yasaitanmen/Speaker-Enclosure/cad/stl/port_tube_150mm.stl

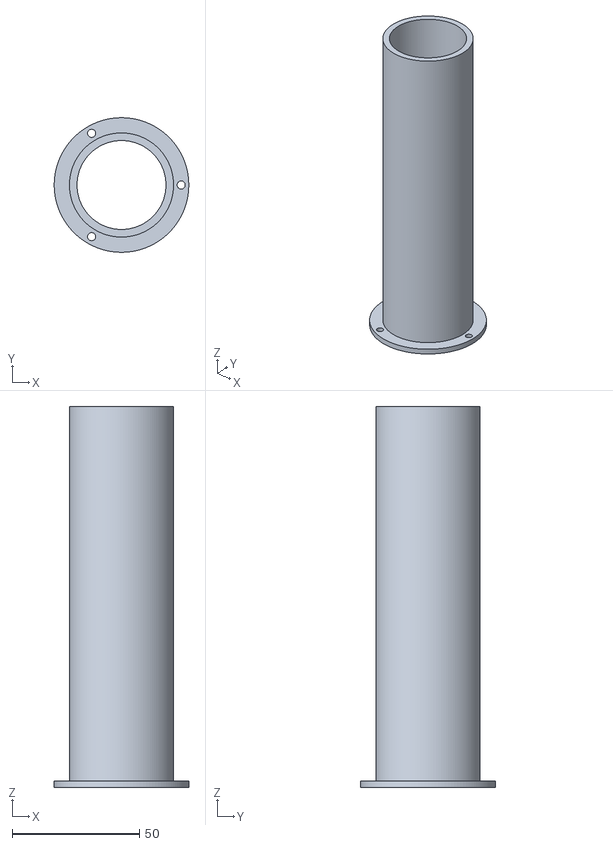
[picture p16: CAD file, 2026-08-31]
cad/stl/port_tube_150mm.stl
53.0 x 53.0 x 150.0
