yasaitanmen/Speaker-Enclosure/cad/stl/5.5L/upper_plate_u4_blank.stl

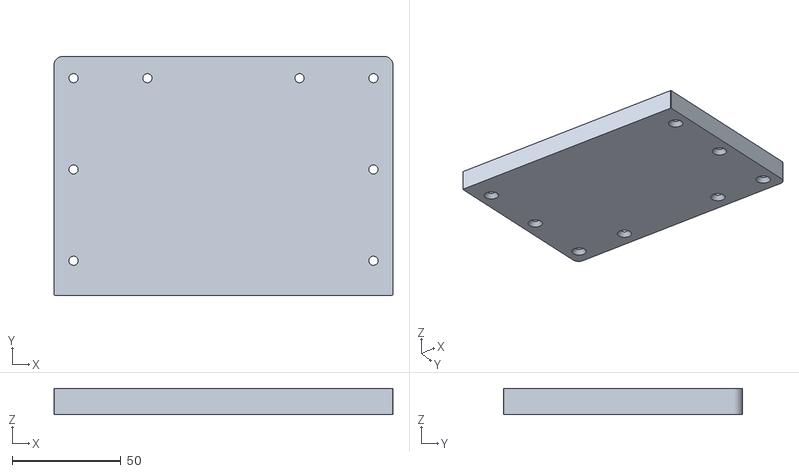
[picture p17: CAD file, 2026-08-31]
cad/stl/5.5L/upper_plate_u4_blank.stl
156.0 x 110.0 x 12.0
