yasaitanmen/Speaker-Enclosure/cad/stl/upper_plate_u2_3inch.stl

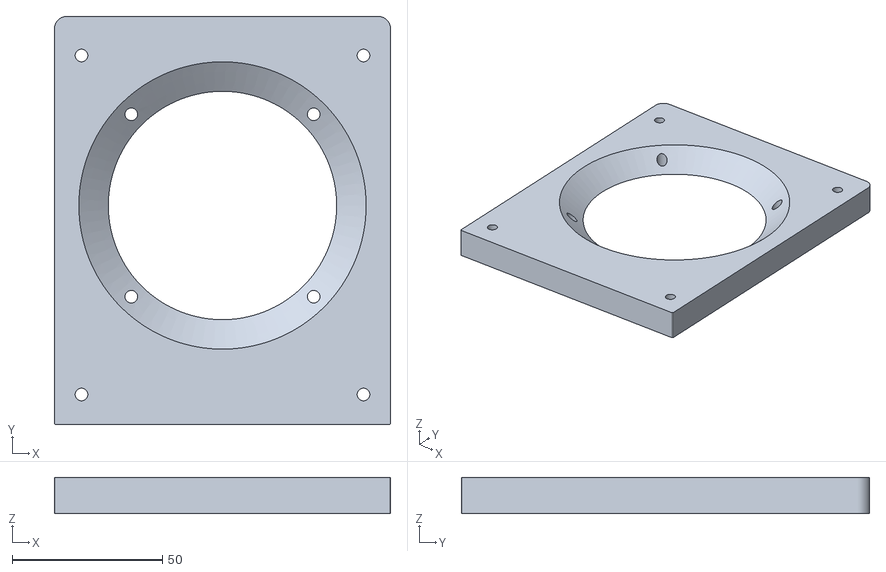
[picture p18: CAD file, 2026-08-31]
cad/stl/upper_plate_u2_3inch.stl
112.0 x 136.0 x 12.0
