yasaitanmen/Speaker-Enclosure/cad/stl/5.5L/upper_plate_u3_4inch.stl

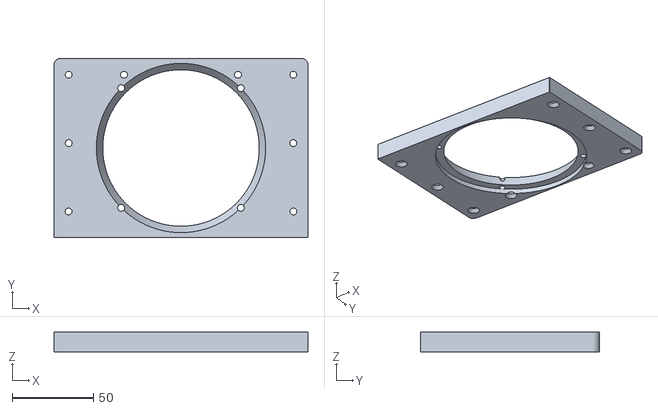
[picture p19: CAD file, 2026-08-31]
cad/stl/5.5L/upper_plate_u3_4inch.stl
156.0 x 110.0 x 12.0
