yasaitanmen/Speaker-Enclosure/cad/stl/port_tube_80mm.stl

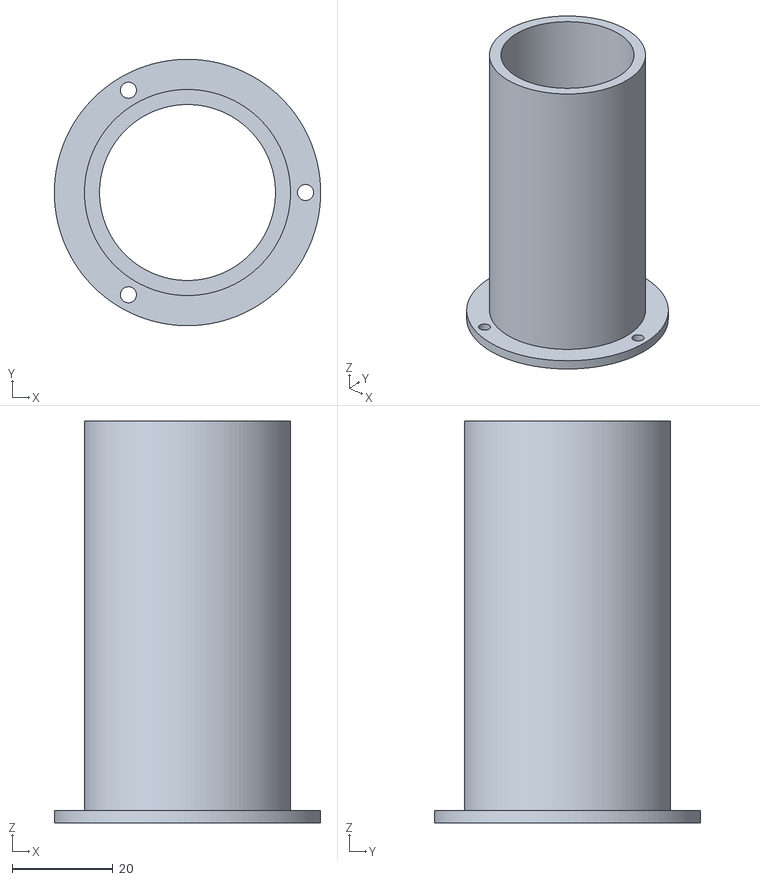
[picture p20: CAD file, 2026-08-31]
cad/stl/port_tube_80mm.stl
53.0 x 53.0 x 80.0
