yasaitanmen/Speaker-Enclosure/cad/stl/upper_gasket_eva.stl

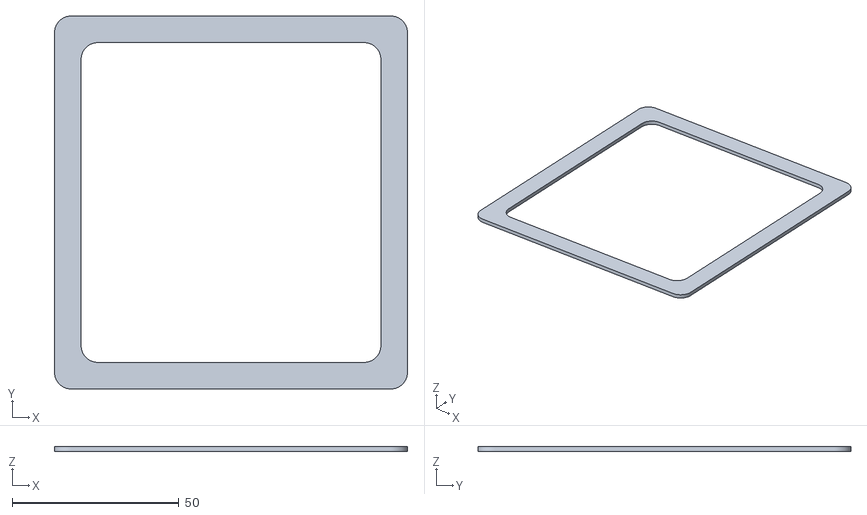
[picture p22: CAD file, 2026-08-31]
cad/stl/upper_gasket_eva.stl
106.0 x 112.0 x 1.50
