yasaitanmen/Speaker-Enclosure/cad/stl/upper_plate_u1_2inch.stl

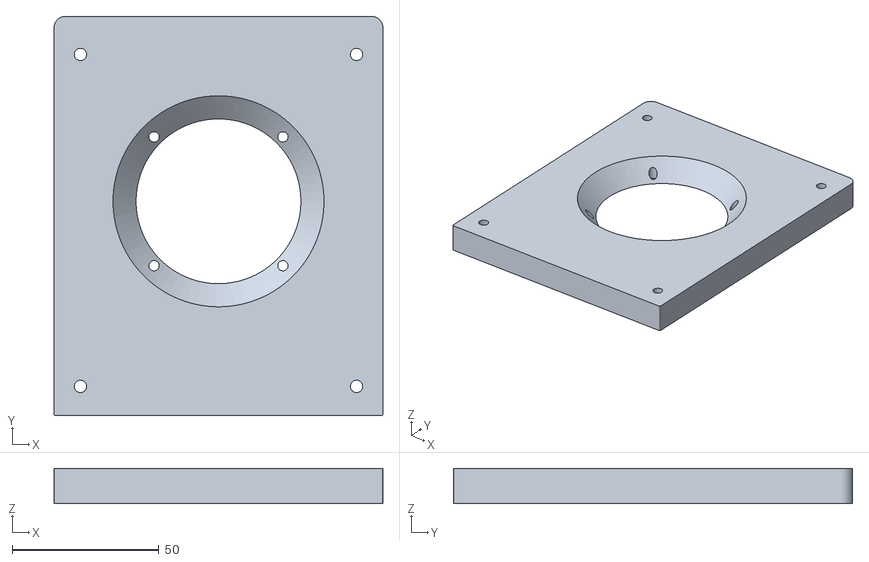
[picture p24: CAD file, 2026-08-31]
cad/stl/upper_plate_u1_2inch.stl
112.0 x 136.0 x 12.0
