yasaitanmen/Speaker-Enclosure/cad/stl/5.5L/lower_plate_55L_p3_slit_port.stl

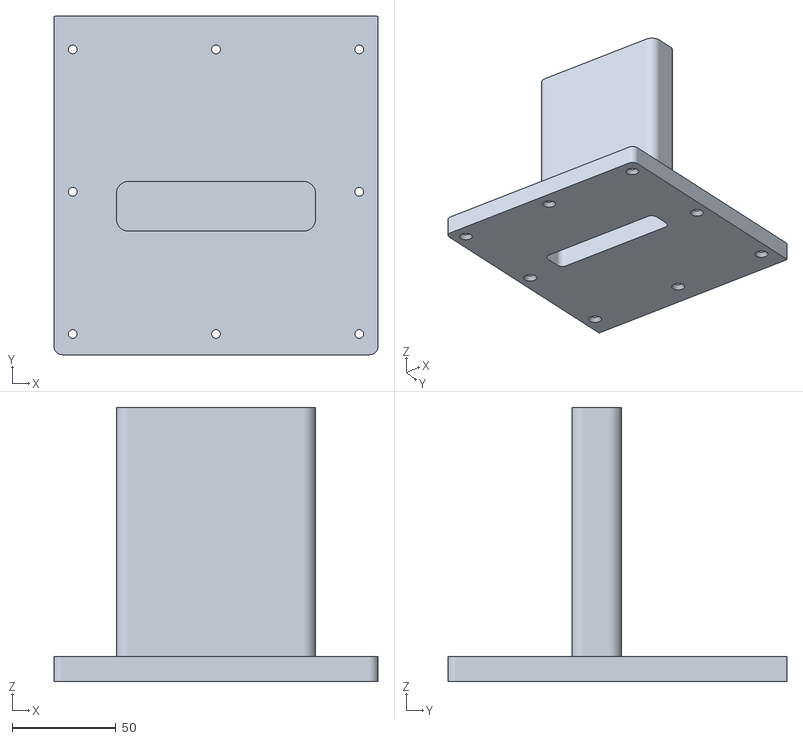
[picture p25: CAD file, 2026-08-31]
cad/stl/5.5L/lower_plate_55L_p3_slit_port.stl
156.0 x 163.0 x 132.0
