yasaitanmen/Speaker-Enclosure/cad/stl/window_brace.stl

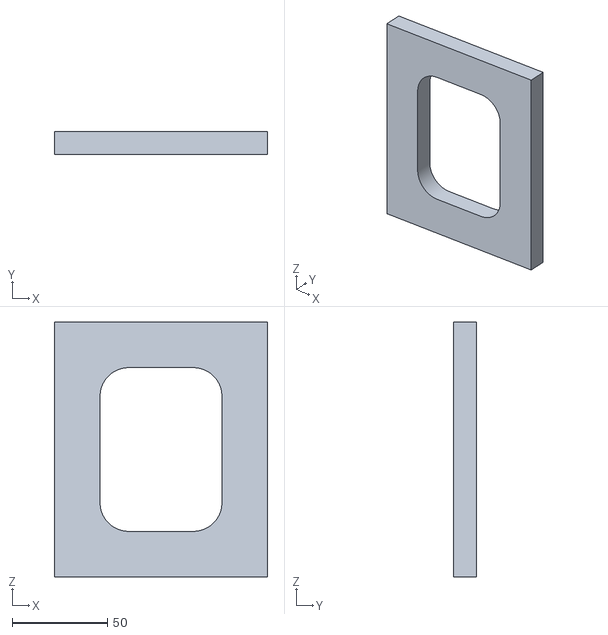
[picture p26: CAD file, 2026-08-31]
cad/stl/window_brace.stl
112.0 x 12.0 x 134.0
