yasaitanmen/Speaker-Enclosure/cad/stl/inner_fixed_baffle_frame.stl

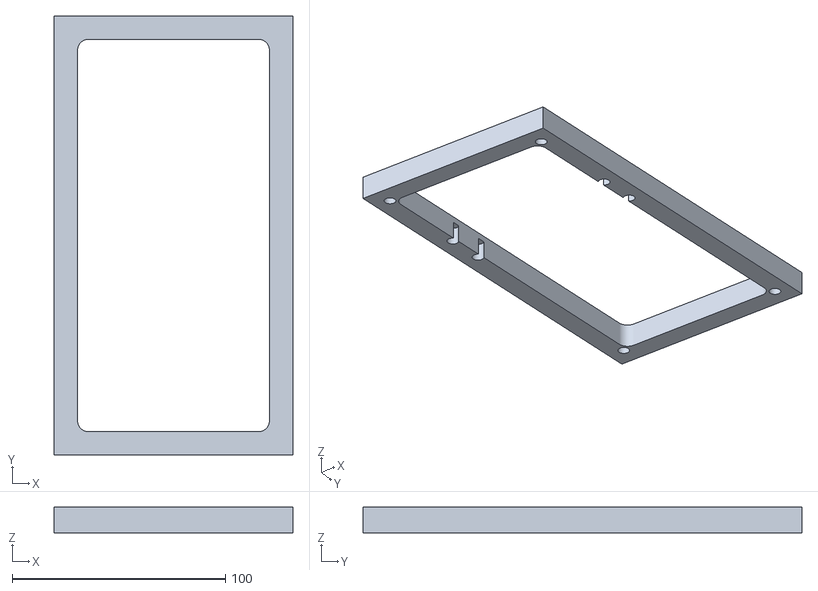
[picture p28: CAD file, 2026-08-31]
cad/stl/inner_fixed_baffle_frame.stl
112.0 x 206.0 x 12.0
