yasaitanmen/Speaker-Enclosure/cad/stl/5.5L/lower_plate_55L_p4_passive_rad.stl

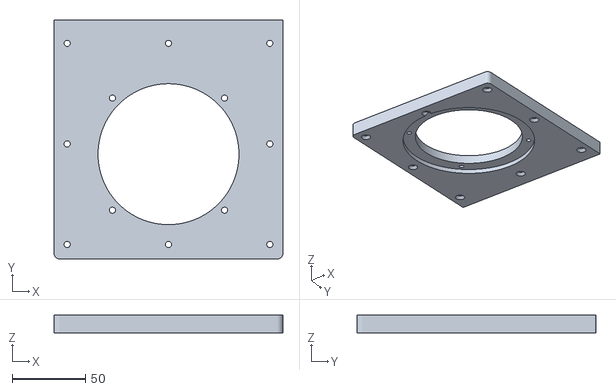
[picture p29: CAD file, 2026-08-31]
cad/stl/5.5L/lower_plate_55L_p4_passive_rad.stl
156.0 x 163.0 x 12.0
