yasaitanmen/Speaker-Enclosure/cad/stl/rear_panel.stl

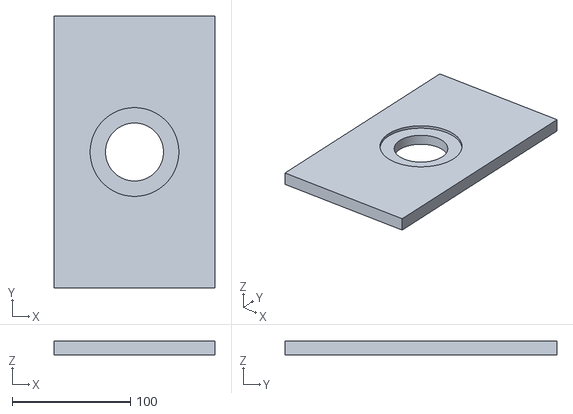
[picture p30: CAD file, 2026-08-31]
cad/stl/rear_panel.stl
136.0 x 230.0 x 12.0
