yasaitanmen/Speaker-Enclosure/cad/stl/lower_gasket_eva.stl

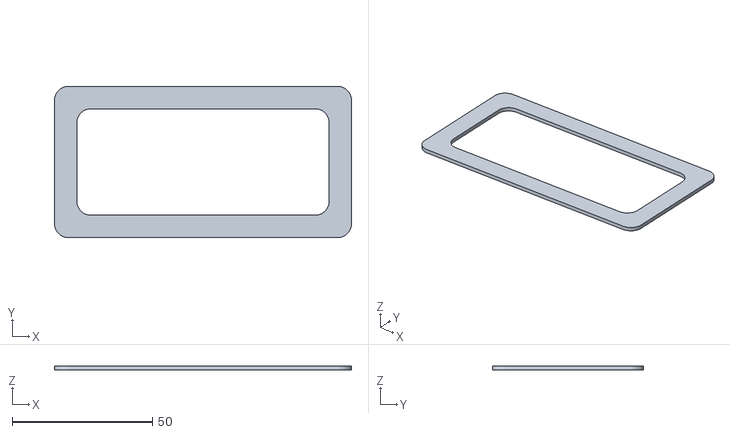
[picture p31: CAD file, 2026-08-31]
cad/stl/lower_gasket_eva.stl
106.0 x 54.0 x 1.50
