yasaitanmen/Speaker-Enclosure/cad/stl/5.5L/internal_hollow_mouth_frame.stl

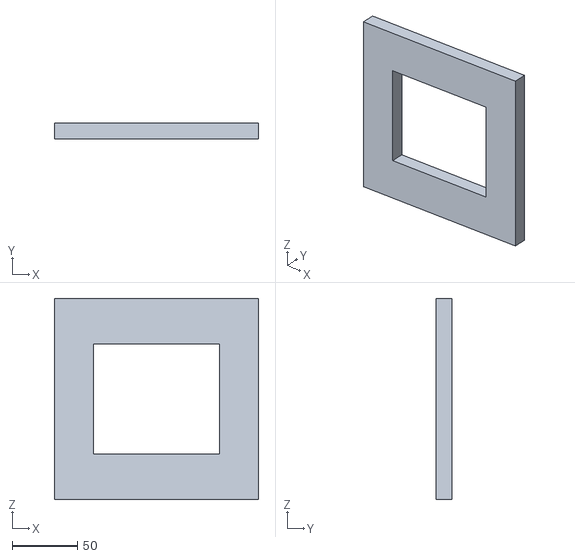
[picture p32: CAD file, 2026-08-31]
cad/stl/5.5L/internal_hollow_mouth_frame.stl
156.0 x 12.0 x 154.0
