yasaitanmen/Speaker-Enclosure/cad/stl/5.5L/removable_dbr_partition_plate.stl

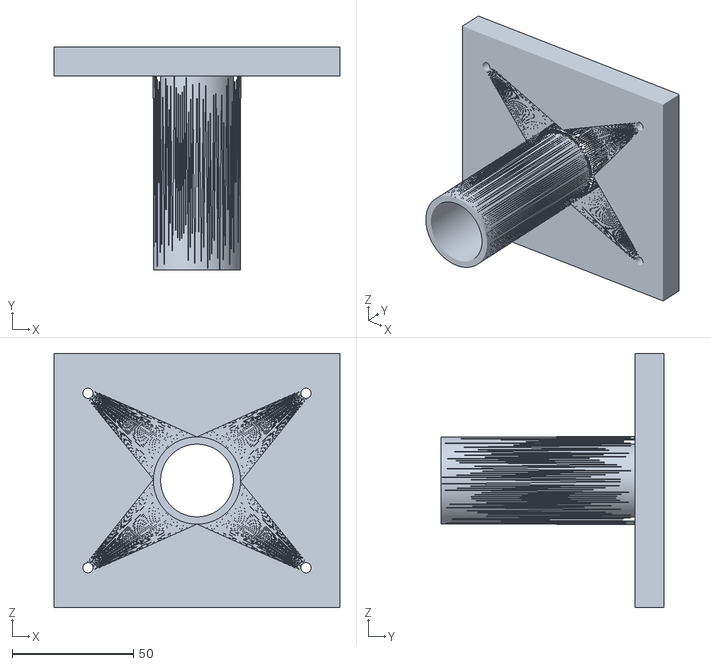
[picture p33: CAD file, 2026-08-31]
cad/stl/5.5L/removable_dbr_partition_plate.stl
118.0 x 92.0 x 105.0
