yasaitanmen/Speaker-Enclosure/cad/stl/lower_plate_p3_slit_port.stl

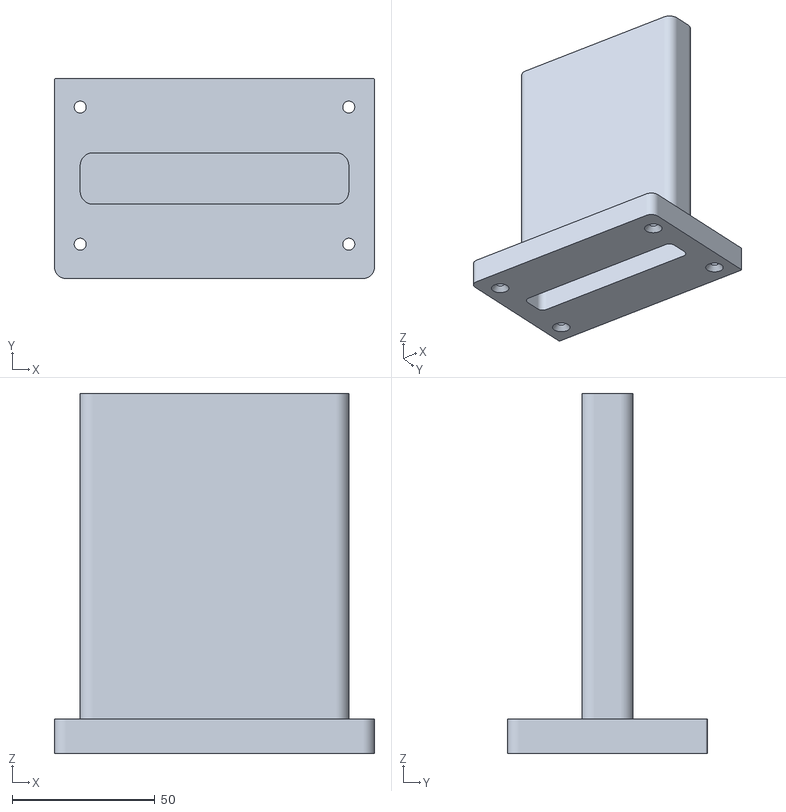
[picture p34: CAD file, 2026-08-31]
cad/stl/lower_plate_p3_slit_port.stl
112.0 x 70.0 x 126.0
