yasaitanmen/Speaker-Enclosure/cad/stl/5.5L/internal_dbr_partition_brace.stl

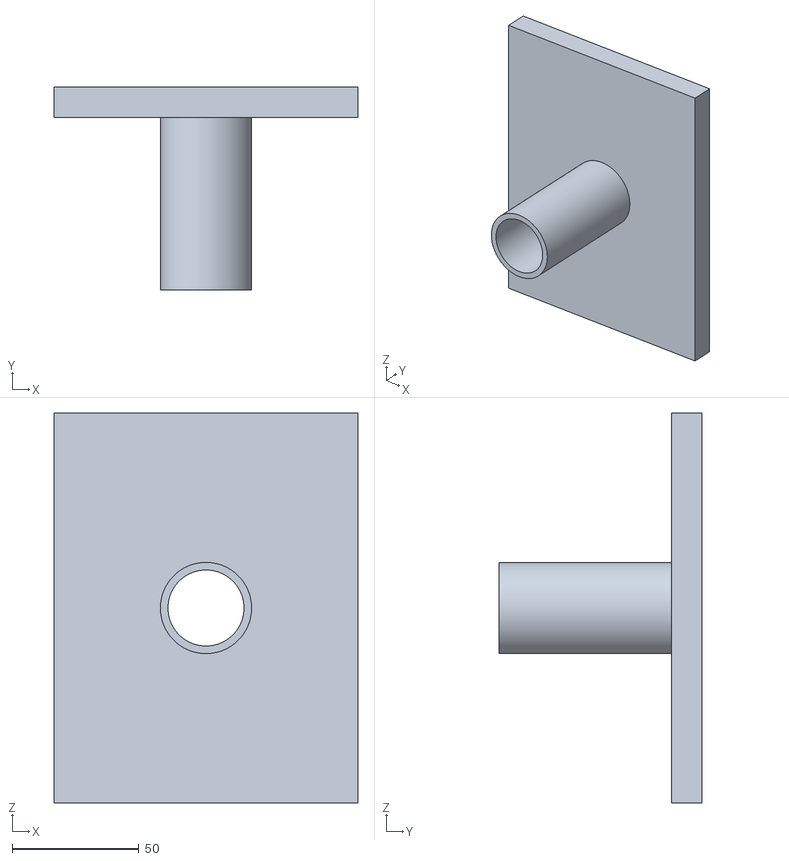
[picture p35: CAD file, 2026-08-31]
cad/stl/5.5L/internal_dbr_partition_brace.stl
120.0 x 80.0 x 154.0
