yasaitanmen/Speaker-Enclosure/cad/stl/upper_plate_u4_blank.stl

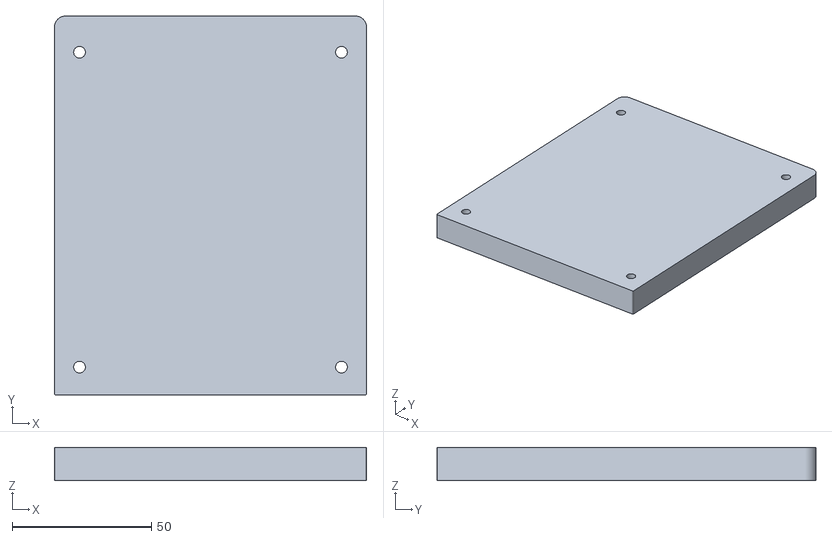
[picture p36: CAD file, 2026-08-31]
cad/stl/upper_plate_u4_blank.stl
112.0 x 136.0 x 12.0
