yasaitanmen/Speaker-Enclosure/cad/stl/5.5L/inner_ladder_baffle_frame_55L.stl

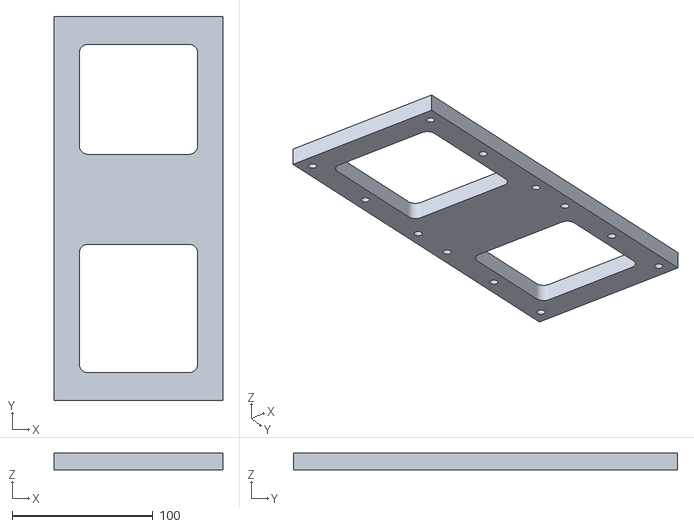
[picture p37: CAD file, 2026-08-31]
cad/stl/5.5L/inner_ladder_baffle_frame_55L.stl
120.0 x 273.0 x 12.0
