yasaitanmen/Speaker-Enclosure/cad/stl/5.5L/ladder_frame_gasket_55L_eva.stl

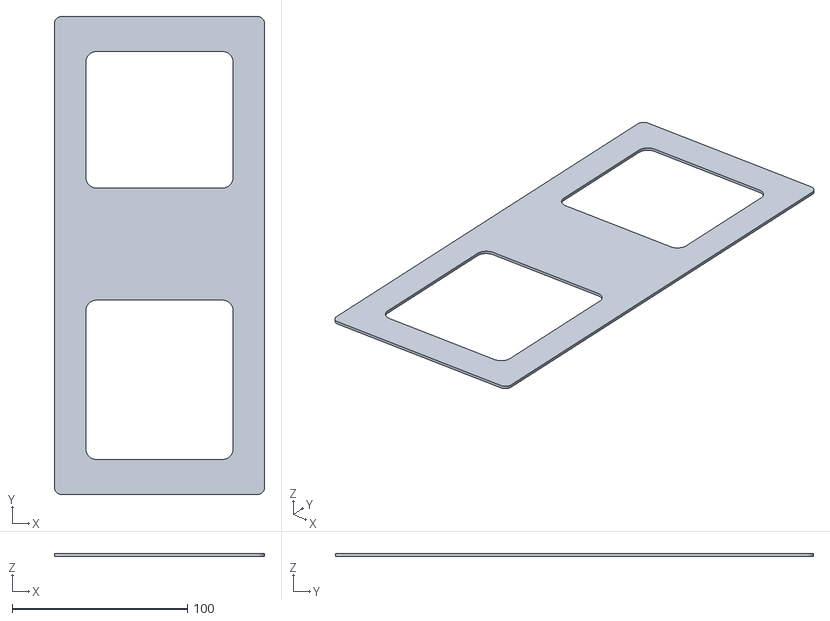
[picture p38: CAD file, 2026-08-31]
cad/stl/5.5L/ladder_frame_gasket_55L_eva.stl
120.0 x 273.0 x 1.50
