yasaitanmen/Speaker-Enclosure/cad/stl/lower_plate_p4_passive_rad.stl

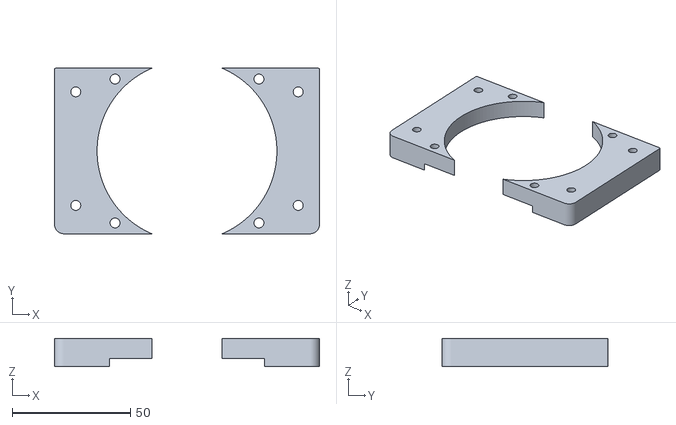
[picture p39: CAD file, 2026-08-31]
cad/stl/lower_plate_p4_passive_rad.stl
112.0 x 70.0 x 12.0
