yasaitanmen/Speaker-Enclosure/cad/stl/5.5L/port_tube_45mm_120mm.stl

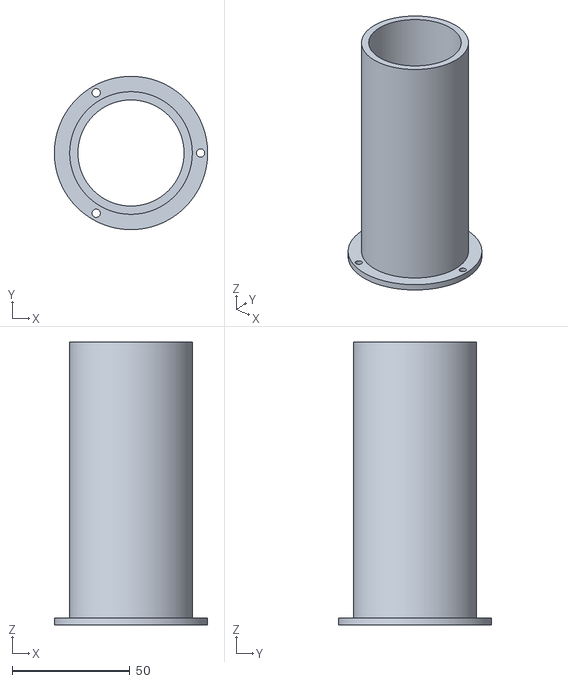
[picture p40: CAD file, 2026-08-31]
cad/stl/5.5L/port_tube_45mm_120mm.stl
65.0 x 65.0 x 120.0
