yasaitanmen/Speaker-Enclosure/cad/stl/upper_plate_u3_4inch.stl

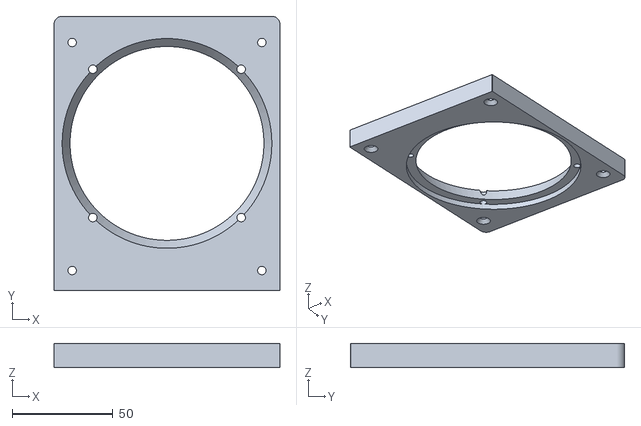
[picture p41: CAD file, 2026-08-31]
cad/stl/upper_plate_u3_4inch.stl
112.0 x 136.0 x 12.0
