yasaitanmen/Speaker-Enclosure/cad/stl/inset_rear_panel.stl

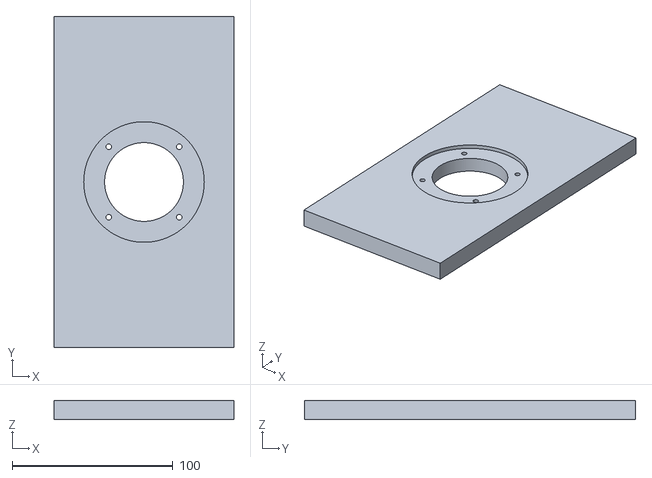
[picture p42: CAD file, 2026-08-31]
cad/stl/inset_rear_panel.stl
112.0 x 206.0 x 12.0
